IndiePandaaaaa/PandaWings-kbd/case/stl/PandaWings_tenting_mounting_wood_screws.stl

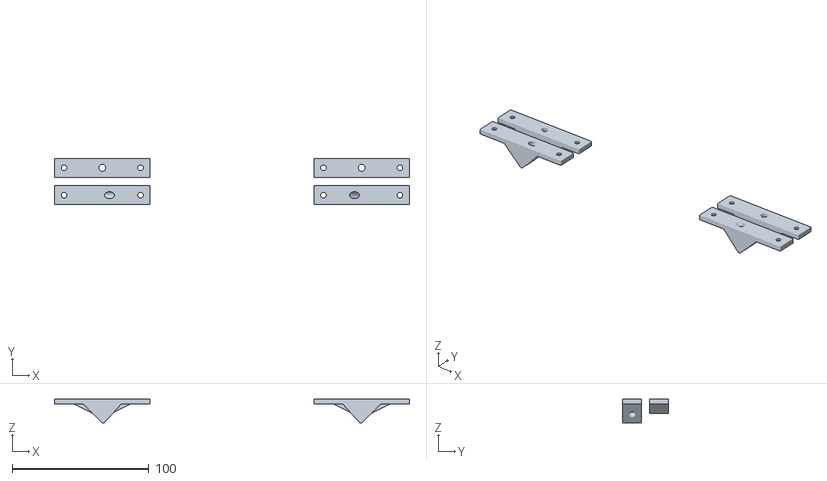
[picture p15: CAD file, 2024-12-21]
case/stl/PandaWings_tenting_mounting_wood_screws.stl
260.0 x 34.0 x 17.5
